74ls00/Speccy2007_128KY/sticker/2.bmp

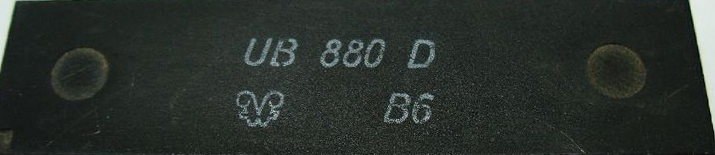
sticker/2.bmp
