74ls00/Speccy2007_128KY/sticker/8.bmp

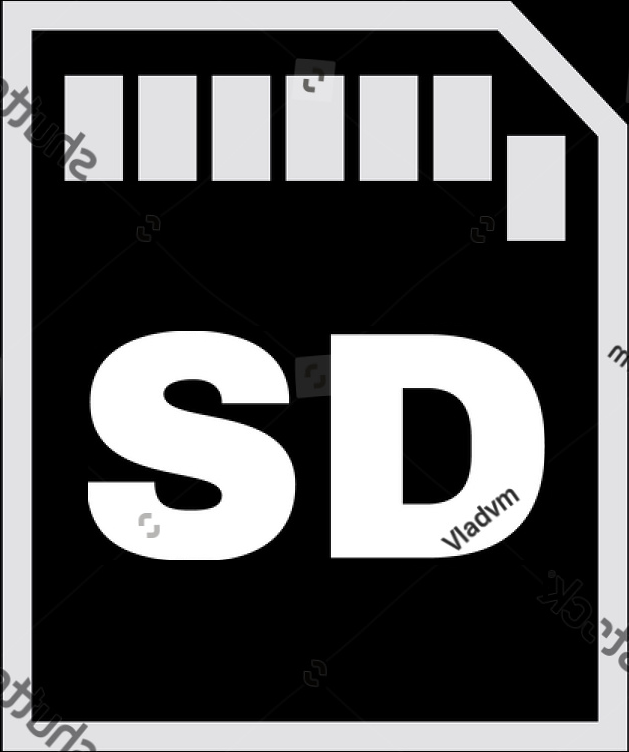
sticker/8.bmp
